ttc002/ROSik/3D/Holder.SLDPRT

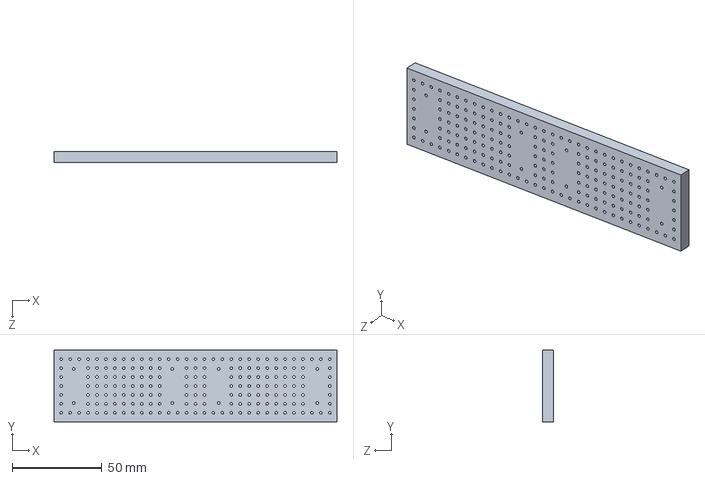
[picture p25: CAD file, 2025-06-23]
3D/Holder.SLDPRT
158.0 x 40.0 x 6.00 mm
