ttc002/ROSik/3D/Braket motor N20 60RPM.SLDPRT

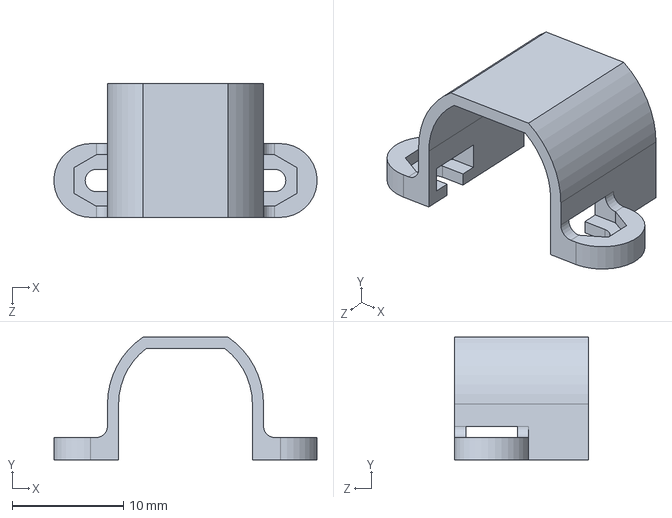
[picture p26: CAD file, 2025-06-23]
3D/Braket motor N20 60RPM.SLDPRT
23.6 x 11.0 x 12.0 mm
