ttc002/ROSik/3D/MINI SWITCH.SLDPRT

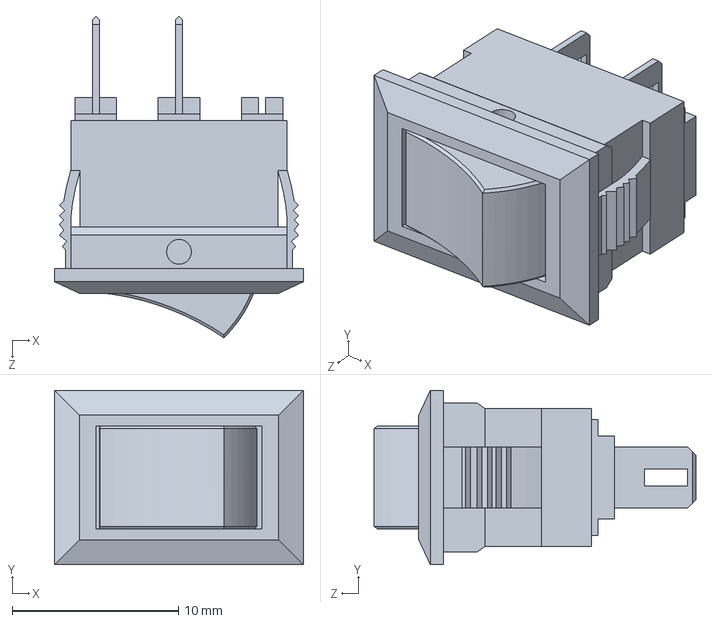
[picture p27: CAD file, 2025-06-23]
3D/MINI SWITCH.SLDPRT
15.0 x 10.5 x 19.4 mm
