ttc002/ROSik/3D/10 - ESPLayer.SLDPRT

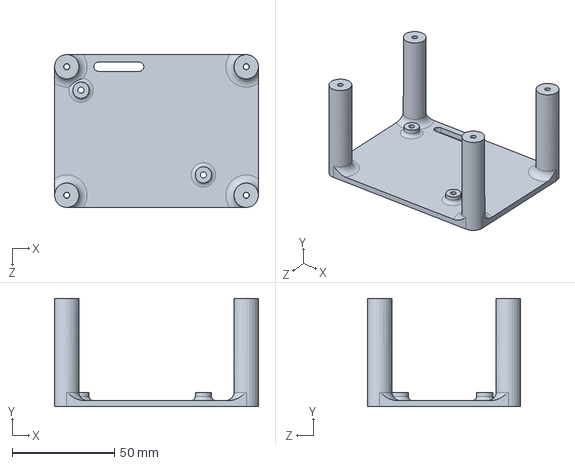
[picture p28: CAD file, 2025-06-23]
3D/10 - ESPLayer.SLDPRT
100.0 x 53.0 x 75.0 mm
