ttc002/ROSik/3D/11 - 8ledHolderTop.SLDPRT

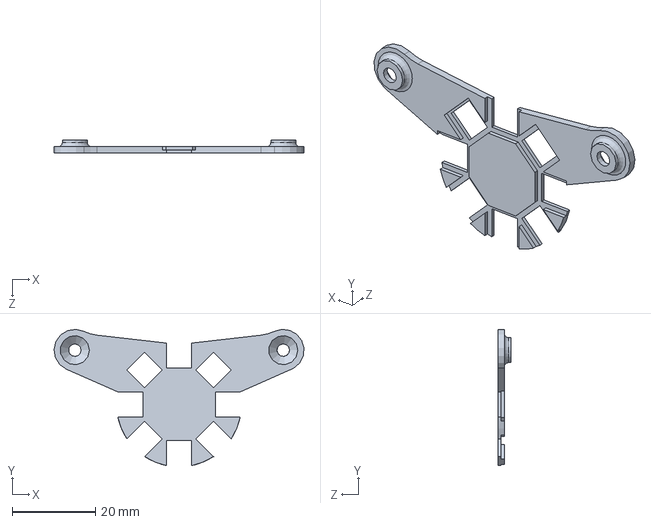
[picture p29: CAD file, 2025-06-23]
3D/11 - 8ledHolderTop.SLDPRT
60.0 x 32.7 x 3.10 mm
