ttc002/ROSik/3D/ydlidar x4.SLDPRT

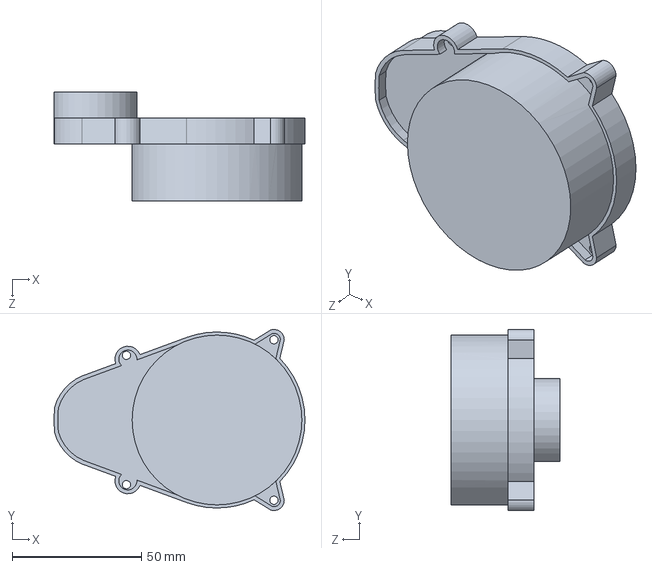
[picture p30: CAD file, 2025-06-23]
3D/ydlidar x4.SLDPRT
97.0 x 70.0 x 42.0 mm
