ttc002/ROSik/esp32_cam/firmware/firmware.ino

#include "esp_camera.h"
#include <WiFi.h>

// ====== Ваши настройки сети ======
const char* ssid = "robotx";
const char* password = "78914040";

// ====== Настройки камеры (не трогать) ======
#define PWDN_GPIO_NUM     32
#define RESET_GPIO_NUM    -1
#define XCLK_GPIO_NUM      0
#define SIOD_GPIO_NUM     26
#define SIOC_GPIO_NUM     27
#define Y9_GPIO_NUM       35
#define Y8_GPIO_NUM       34
#define Y7_GPIO_NUM       39
#define Y6_GPIO_NUM       36
#define Y5_GPIO_NUM       21
#define Y4_GPIO_NUM       19
#define Y3_GPIO_NUM       18
#define Y2_GPIO_NUM        5
#define VSYNC_GPIO_NUM    25
#define HREF_GPIO_NUM     23
#define PCLK_GPIO_NUM     22

// Параметры изображения
#define FRAME_SIZE        FRAMESIZE_VGA
#define JPEG_QUALITY      12

// Создаём TCP-сервер на порту 80
WiFiServer server(80);

void setup() {
  // Инициализация UART для отладки
  Serial.begin(115200);
  while (!Serial) { delay(10); }

  // Подключаемся к Wi-Fi
  WiFi.begin(ssid, password);
  Serial.printf("Connecting to WiFi: %s", ssid);
  while (WiFi.status() != WL_CONNECTED) {
    delay(500);
    Serial.print(".");
  }
  Serial.println();
  Serial.printf("WiFi connected. IP address: %s\n", WiFi.localIP().toString().c_str());

  // Инициализация камеры
  camera_config_t config;
  config.ledc_channel = LEDC_CHANNEL_0;
  config.ledc_timer   = LEDC_TIMER_0;
  config.pin_d0       = Y2_GPIO_NUM;
  config.pin_d1       = Y3_GPIO_NUM;
  config.pin_d2       = Y4_GPIO_NUM;
  config.pin_d3       = Y5_GPIO_NUM;
  config.pin_d4       = Y6_GPIO_NUM;
  config.pin_d5       = Y7_GPIO_NUM;
  config.pin_d6       = Y8_GPIO_NUM;
  config.pin_d7       = Y9_GPIO_NUM;
  config.pin_xclk     = XCLK_GPIO_NUM;
  config.pin_pclk     = PCLK_GPIO_NUM;
  config.pin_vsync    = VSYNC_GPIO_NUM;
  config.pin_href     = HREF_GPIO_NUM;
  config.pin_sscb_sda = SIOD_GPIO_NUM;
  config.pin_sscb_scl = SIOC_GPIO_NUM;
  config.pin_pwdn     = PWDN_GPIO_NUM;
  config.pin_reset    = RESET_GPIO_NUM;
  config.xclk_freq_hz = 20000000;
  config.pixel_format = PIXFORMAT_JPEG;

  if (psramFound()) {
    config.frame_size   = FRAME_SIZE;
    config.jpeg_quality = JPEG_QUALITY;
    config.fb_count     = 2;
  } else {
    config.frame_size   = FRAMESIZE_SVGA;
    config.jpeg_quality = max(JPEG_QUALITY, 12);
    config.fb_count     = 1;
  }

  if (esp_camera_init(&config) != ESP_OK) {
    Serial.println("Camera init failed");
    return;
  }
  Serial.println("Camera init OK");

  // Запускаем сервер
  server.begin();
  Serial.println("HTTP MJPEG stream ready at http://<IP>/stream");
}

void loop() {
  WiFiClient client = server.available();
  if (client) {
    Serial.println("Client connected");
    // Отправляем HTTP-заголовки
    client.printf(
      "HTTP/1.1 200 OK\r\n"
      "Content-Type: multipart/x-mixed-replace; boundary=frame\r\n"
      "Access-Control-Allow-Origin: *\r\n"
      "\r\n"
    );

    while (client.connected()) {
      camera_fb_t *fb = esp_camera_fb_get();
      if (!fb) break;

      // Заголовок каждого кадра
      client.printf(
        "--frame\r\n"
        "Content-Type: image/jpeg\r\n"
        "Content-Length: %u\r\n\r\n",
        fb->len
      );
      // Данные JPEG
      client.write(fb->buf, fb->len);
      client.write("\r\n", 2);

      esp_camera_fb_return(fb);
      delay(100); // ~10 fps
    }

    client.stop();
    Serial.println("Client disconnected");
  }
}
